TinyCircuits/TinyCircuits-Whisker-Temp-Press-Hum-VOC-AST1036/images/AST1036-Tutorial-Image-01.png

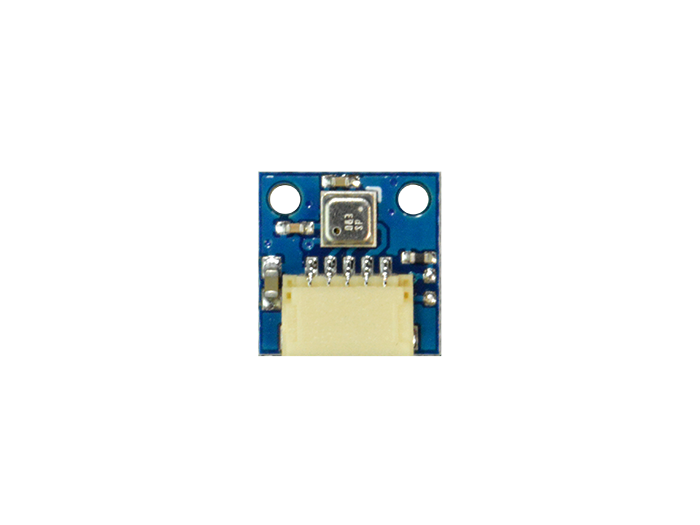
images/AST1036-Tutorial-Image-01.png
