TinyCircuits/TinyCircuits-Whisker-Temp-Press-Hum-VOC-AST1036/images/AST1036-Tutorial-Image-03.png

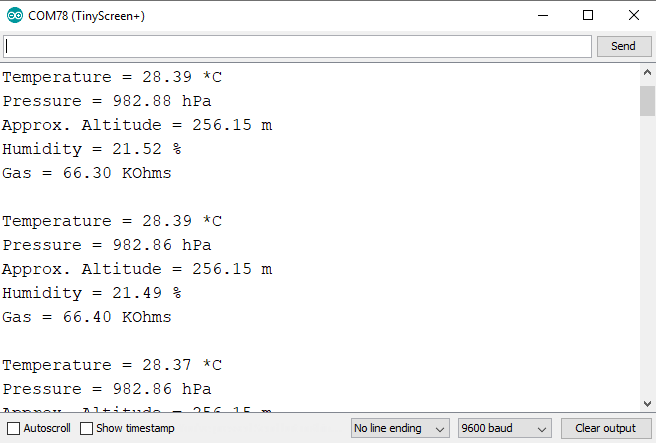
images/AST1036-Tutorial-Image-03.png
